bkshepherd/DaisySeedProjects/Hardware/GuitarPedal1590b-SMD/docs/images/Backside.png

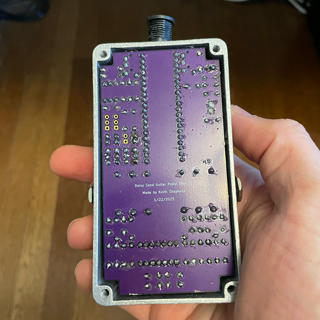
Hardware/GuitarPedal1590b-SMD/docs/images/Backside.png
