bkshepherd/DaisySeedProjects/Software/GuitarPedal/Effect-Modules/fm_keys_module.cpp

#include "fm_keys_module.h"
#include "../Util/audio_utilities.h"
#include <array>

using namespace bkshepherd;

// static VoiceManager<18> voice_handler; // starting with 1 voice for testing, 16 WORKS, 18 freezes
//  With added carrier env control, 16 glitches, 12 works
//  moved param changing to outside function, can run 18

static const auto s_metaData = [] {
    std::array<ParameterMetaData, FmKeysModule::PARAM_COUNT> params{};

    params[FmKeysModule::LEVEL] = {
        name : "Level",
        valueType : ParameterValueType::Float,
        defaultValue : {.float_value = 0.5f},
        knobMapping : 0,
        midiCCMapping : 14
    };

    params[FmKeysModule::RATIO] = {
        name : "Ratio",
        valueType : ParameterValueType::Float,
        defaultValue : {.float_value = 1.0f},
        knobMapping : 1,
        midiCCMapping : 15,
        minValue : 0,
        maxValue : 16
    };

    params[FmKeysModule::MOD_LEVEL] = {
        name : "ModLevel",
        valueType : ParameterValueType::Float,
        defaultValue : {.float_value = 0.2f},
        knobMapping : 2,
        midiCCMapping : 16
    };

    params[FmKeysModule::MOD_RATIO] = {
        name : "ModRatio",
        valueType : ParameterValueType::Float,
        defaultValue : {.float_value = 16.0f},
        knobMapping : 3,
        midiCCMapping : 17,
        minValue : 0,
        maxValue : 16
    };

    // TODO: Try fine/coarse step sizes of 0.5 (not in lighthouse yet?)
    params[FmKeysModule::CAR_ATTACK] = {
        name : "CarAttack",
        valueType : ParameterValueType::Float,
        defaultValue : {.float_value = 0.5f},
        knobMapping : 4,
        midiCCMapping : 18
    };

    params[FmKeysModule::CAR_DECAY] = {
        name : "CarDecay",
        valueType : ParameterValueType::Float,
        defaultValue : {.float_value = 0.5f},
        knobMapping : 5,
        midiCCMapping : 19
    };

    params[FmKeysModule::CAR_SUSTAIN] = {
        name : "CarSustain",
        valueType : ParameterValueType::Float,
        defaultValue : {.float_value = 0.5f},
        knobMapping : -1,
        midiCCMapping : 20
    };

    params[FmKeysModule::CAR_RELEASE] = {
        name : "CarRelease",
        valueType : ParameterValueType::Float,
        defaultValue : {.float_value = 0.5f},
        knobMapping : -1,
        midiCCMapping : 21
    };

    params[FmKeysModule::MOD_ATTACK] = {
        name : "ModAttack",
        valueType : ParameterValueType::Float,
        defaultValue : {.float_value = 0.5f},
        knobMapping : -1,
        midiCCMapping : 22
    };

    params[FmKeysModule::MOD_DECAY] = {
        name : "ModDecay",
        valueType : ParameterValueType::Float,
        defaultValue : {.float_value = 0.5f},
        knobMapping : -1,
        midiCCMapping : 23
    };

    params[FmKeysModule::MOD_SUSTAIN] = {
        name : "ModSustain",
        valueType : ParameterValueType::Float,
        defaultValue : {.float_value = 0.5f},
        knobMapping : -1,
        midiCCMapping : 24
    };

    params[FmKeysModule::MOD_RELEASE] = {
        name : "ModRelease",
        valueType : ParameterValueType::Float,
        defaultValue : {.float_value = 0.5f},
        knobMapping : -1,
        midiCCMapping : 25
    };

    return params;
}();

// Default Constructor
FmKeysModule::FmKeysModule() : BaseEffectModule(), m_freqMin(250.0f), m_freqMax(16000.0f), m_cachedEffectMagnitudeValue(1.0f) {
    // Set the name of the effect
    m_name = "FmKeys";

    // Setup the meta data reference for this Effect
    m_paramMetaData = s_metaData.data();

    // Initialize Parameters for this Effect
    this->InitParams(static_cast<int>(s_metaData.size()));
}

// Destructor
FmKeysModule::~FmKeysModule() {
    // No Code Needed
}

void FmKeysModule::Init(float sample_rate) {
    BaseEffectModule::Init(sample_rate);

    m_voice_handler.Init(sample_rate);
}

void FmKeysModule::ParameterChanged(int parameter_id) {

    if (parameter_id == LEVEL) {
        m_voice_handler.SetCarrierLevel(GetParameterAsFloat(LEVEL));

    } else if (parameter_id == RATIO) {
        float temp = GetParameterAsFloat(RATIO) * 2; // scale 0 to 16... 0 to 32
        int temp2 = static_cast<int>(temp);      // round by converting to int
        float temp3 = static_cast<float>(temp2);
        float float_val = temp3 / 2.0; // 0 to 16 increments of 0.5
        m_voice_handler.SetCarrierRatio(float_val);

    } else if (parameter_id == MOD_LEVEL) {
        m_voice_handler.SetModulatorLevel(GetParameterAsFloat(MOD_LEVEL) * GetParameterAsFloat(MOD_LEVEL)); // exponential

    } else if (parameter_id == MOD_RATIO) {
        float temp = GetParameterAsFloat(MOD_RATIO) * 2; // scale 0 to 16... 0 to 32
        int temp2 = static_cast<int>(temp);      // round by converting to int
        float temp3 = static_cast<float>(temp2);
        float float_val = temp3 / 2.0; // 0 to 16 increments of 0.5
        m_voice_handler.SetModulatorRatio(float_val);

    } else if (parameter_id == CAR_ATTACK) {
        m_voice_handler.SetCarrierAttack(GetParameterAsFloat(CAR_ATTACK) * GetParameterAsFloat(CAR_ATTACK) * 0.9999 + 0.0001); // exponential

    } else if (parameter_id == CAR_DECAY) {
        m_voice_handler.SetCarrierDecay(GetParameterAsFloat(CAR_DECAY) * GetParameterAsFloat(CAR_DECAY) * 0.9999 + 0.0001); // exponential

    } else if (parameter_id == CAR_SUSTAIN) {
        m_voice_handler.SetCarrierSustain(GetParameterAsFloat(CAR_SUSTAIN) * 0.999 + 0.001);

    } else if (parameter_id == CAR_RELEASE) {
        m_voice_handler.SetCarrierRelease(GetParameterAsFloat(CAR_RELEASE) * 0.999 + 0.001);

    } else if (parameter_id == MOD_ATTACK) {
        m_voice_handler.SetModAttack(GetParameterAsFloat(MOD_ATTACK) * GetParameterAsFloat(MOD_ATTACK) * 0.9999 + 0.0001); // exponential

    } else if (parameter_id == MOD_DECAY) {
        m_voice_handler.SetModDecay(GetParameterAsFloat(MOD_DECAY) * GetParameterAsFloat(MOD_DECAY) * 0.9999 + 0.0001); // exponential

    } else if (parameter_id == MOD_SUSTAIN) {
        m_voice_handler.SetModSustain(GetParameterAsFloat(MOD_SUSTAIN) * 0.999 + 0.001);

    } else if (parameter_id == MOD_RELEASE) {
        m_voice_handler.SetModRelease(GetParameterAsFloat(MOD_RELEASE) * 0.999 + 0.001);
    }
}

void FmKeysModule::OnNoteOn(float notenumber, float velocity) {
    // Note Off can come in as Note On w/ 0 Velocity
    if (velocity == 0.f) {
        m_voice_handler.OnNoteOff(notenumber, velocity);
    } else {
        m_voice_handler.OnNoteOn(notenumber, velocity);
    }
}

void FmKeysModule::OnNoteOff(float notenumber, float velocity) { m_voice_handler.OnNoteOff(notenumber, velocity); }

void FmKeysModule::ProcessMono(float in) {
    BaseEffectModule::ProcessMono(in);

    // float through_audioL = m_audioLeft;

    float sum = 0.f;
    sum = m_voice_handler.Process() * 0.3f; // 0.3 for volume reduction
    m_audioLeft = sum;
    m_audioRight = m_audioLeft;
}

void FmKeysModule::ProcessStereo(float inL, float inR) {
    // Calculate the mono effect
    ProcessMono(inL);
}

float FmKeysModule::GetBrightnessForLED(int led_id) const {
    float value = BaseEffectModule::GetBrightnessForLED(led_id);

    if (led_id == 1) {
        return value * m_cachedEffectMagnitudeValue;
    }

    return value;
}
