bkshepherd/DaisySeedProjects/Software/GuitarPedal/Effect-Modules/nam_module.cpp

#include "nam_module.h"
#include "../Util/audio_utilities.h"
#include "../dependencies/RTNeural-NAM-modified/wavenet/wavenet_model.hpp"
#include "Nam/model_data_nam.h"
#include <RTNeural/RTNeural.h>
#include <q/fx/biquad.hpp>
#include <array>

using namespace bkshepherd;

constexpr uint8_t NUM_FILTERS_NAM = 3;

const float minGain = -10.f;
const float maxGain = 10.f;

const float centerFrequencyNam[NUM_FILTERS_NAM] = {110.f, 900.f, 4000.f}; // Experiment with these freqs and q values
const float q_nam[NUM_FILTERS_NAM] = {.7f, .7f, .7f};

cycfi::q::peaking filter_nam[NUM_FILTERS_NAM] = {{0, centerFrequencyNam[0], 48000, q_nam[0]},
                                                 {0, centerFrequencyNam[1], 48000, q_nam[1]},
                                                 {0, centerFrequencyNam[2], 48000, q_nam[2]}};

// This must match the length of the model_collection_nam array in model_data_nam.h
const size_t k_numModels = 10;

static const char *s_modelBinNames[k_numModels] = {
    "Mesa", "Match30", "DumHighG", "DumLowG", "Ethos", "Splawn", "PRSArch", "JCM800", "SansAmp", "BE-100",
};
struct NAMMathsProvider {
#if RTNEURAL_USE_EIGEN
    template <typename Matrix> static auto tanh(const Matrix &x) {
        // See: math_approx::tanh<3>
        const auto x_poly = x.array() * (1.0f + 0.183428244899f * x.array().square());
        return x_poly.array() * (x_poly.array().square() + 1.0f).array().rsqrt();
        // return x.array().tanh(); // Tried using Eigen's built in tanh(), also works, failed on the same larger models as above
        // custom tanh
    }
#elif RTNEURAL_USE_XSIMD
    template <typename T> static T tanh(const T &x) { return math_approx::tanh<3>(x); }
#endif
};

static const auto s_metaData = [] {
    std::array<ParameterMetaData, NamModule::PARAM_COUNT> params{};

    params[NamModule::GAIN] = {
        name : "Gain",
        valueType : ParameterValueType::Float,
        valueCurve : ParameterValueCurve::Log,
        defaultValue : {.float_value = 0.5f},
        knobMapping : 0,
        midiCCMapping : 14,
    };

    params[NamModule::LEVEL] = {
        name : "Level",
        valueType : ParameterValueType::Float,
        defaultValue : {.float_value = 0.5f},
        knobMapping : 1,
        midiCCMapping : 15
    };

    params[NamModule::MODEL] = {
        name : "Model",
        valueType : ParameterValueType::Binned,
        valueBinCount : k_numModels,
        valueBinNames : s_modelBinNames,
        defaultValue : {.uint_value = 0},
        knobMapping : 2,
        midiCCMapping : 16
    };

    params[NamModule::BASS] = {
        name : "Bass",
        valueType : ParameterValueType::Float,
        valueBinCount : 0,
        defaultValue : {.float_value = 0.0f},
        knobMapping : 3,
        midiCCMapping : 17,
        minValue : static_cast<int>(minGain),
        maxValue : static_cast<int>(maxGain)
    };

    params[NamModule::MID] = {
        name : "Mid",
        valueType : ParameterValueType::Float,
        valueBinCount : 0,
        defaultValue : {.float_value = 0.0f},
        knobMapping : 4,
        midiCCMapping : 18,
        minValue : static_cast<int>(minGain),
        maxValue : static_cast<int>(maxGain)
    };

    params[NamModule::TREBLE] = {
        name : "Treble",
        valueType : ParameterValueType::Float,
        valueBinCount : 0,
        defaultValue : {.float_value = 0.0f},
        knobMapping : 5,
        midiCCMapping : 19,
        minValue : static_cast<int>(minGain),
        maxValue : static_cast<int>(maxGain)
    };

    params[NamModule::NEURAL_MODEL] = {
        name : "NeuralModel",
        valueType : ParameterValueType::Bool,
        valueBinCount : 0,
        defaultValue : {.uint_value = 1},
        knobMapping : -1,
        midiCCMapping : 20
    };

    params[NamModule::EQ] = {
        name : "EQ",
        valueType : ParameterValueType::Bool,
        valueBinCount : 0,
        defaultValue : {.uint_value = 1},
        knobMapping : -1,
        midiCCMapping : 21
    };

    return params;
}();

// NOTE NAM Standard arch?
/*
using Dilations = wavenet::Dilations<1, 2, 4, 8, 16, 32, 64, 128, 256, 512>;
wavenet::Wavenet_Model<float,
                       1,
                       wavenet::Layer_Array<float, 1, 1, 8, 16, 3, Dilations, false, NAMMathsProvider>,
                       wavenet::Layer_Array<float, 16, 1, 1, 8, 3, Dilations, true, NAMMathsProvider>>
    rtneural_wavenet;
*/

// NOTE NAM "Pico" (unnoficial model type)
using Dilations = wavenet::Dilations<1, 2, 4, 8, 16, 32, 64>;
using Dilations2 = wavenet::Dilations<128, 256, 512, 1, 2, 4, 8, 16, 32, 64, 128, 256, 512>;
wavenet::Wavenet_Model<float, 1, wavenet::Layer_Array<float, 1, 1, 2, 2, 3, Dilations, false, NAMMathsProvider>,
                       wavenet::Layer_Array<float, 2, 1, 1, 2, 3, Dilations2, true, NAMMathsProvider>>
    rtneural_wavenet;

// NOTES:
// nano models:
//   Seems to run (verify sound) for Samplerate 32kHz, Blocksize 64, 1 sample at a time
//   Freezes at Samplerate 48kHz, Blocksize 64, 1 sample at a time
//   Runs at samplerate 32kHz, Blocksize 48, 1 sample, verify sound

// Default Constructor
NamModule::NamModule()
    : BaseEffectModule(), m_gainMin(0.0f), m_gainMax(2.0f), m_levelMin(0.0f), m_levelMax(2.0f), m_cachedEffectMagnitudeValue(1.0f) {
    // Set the name of the effect
    m_name = "NAM";

    // Setup the meta data reference for this Effect
    m_paramMetaData = s_metaData.data();

    // Initialize Parameters for this Effect
    this->InitParams(static_cast<int>(s_metaData.size()));
}

// Destructor
NamModule::~NamModule() {
    // No Code Needed
}

void NamModule::Init(float sample_rate) {
    BaseEffectModule::Init(sample_rate);
    setupWeightsNam(); // in the model data nam .h file
    SelectModel();

    filter_nam[0].config(GetParameterAsFloat(BASS), centerFrequencyNam[0], sample_rate, q_nam[0]);
    filter_nam[1].config(GetParameterAsFloat(MID), centerFrequencyNam[1], sample_rate, q_nam[1]);
    filter_nam[2].config(GetParameterAsFloat(TREBLE), centerFrequencyNam[2], sample_rate, q_nam[2]);
}

void NamModule::ParameterChanged(int parameter_id) {
    if (parameter_id == MODEL) { // Change Model
        SelectModel();
    } else if (parameter_id == BASS) {
        filter_nam[0].config(GetParameterAsFloat(BASS), centerFrequencyNam[0], GetSampleRate(), q_nam[0]);
    } else if (parameter_id == MID) {
        filter_nam[1].config(GetParameterAsFloat(MID), centerFrequencyNam[1], GetSampleRate(), q_nam[1]);
    } else if (parameter_id == TREBLE) {
        filter_nam[2].config(GetParameterAsFloat(TREBLE), centerFrequencyNam[2], GetSampleRate(), q_nam[2]);
    }
}

void NamModule::SelectModel() {
    const int modelIndex = GetParameterAsBinnedValue(MODEL) - 1;

    if (m_currentModelindex != modelIndex) {
        // Temporarily disable output as we switch models
        m_muteOutput = true;
        rtneural_wavenet.load_weights(model_collection_nam[modelIndex].weights);
        static constexpr size_t N = 1; // number of samples sent through model at once
        rtneural_wavenet.prepare(N);   // This is needed, including this allowed the led to come on before freezing
        rtneural_wavenet.prewarm();    // Note: looks like this just sends some 0's through the model
        m_currentModelindex = modelIndex;
        // Re-enable output
        m_muteOutput = false;
    }
}

void NamModule::ProcessMono(float in) {
    // When switching models, we stop processing temporarily and mute the output
    if (m_muteOutput) {
        m_audioLeft = m_audioRight = 0.0f;
        return;
    }

    BaseEffectModule::ProcessMono(in);

    float ampOut;
    float input_arr[1] = {0.0}; // Neural Net Input
    input_arr[0] = m_audioLeft * (m_gainMin + (m_gainMax - m_gainMin) * GetParameterAsFloat(GAIN));

    // NEURAL MODEL //
    if (GetParameterAsBool(NEURAL_MODEL)) {
        ampOut =
            rtneural_wavenet.forward(input_arr[0]) * 0.4; // TODO Try this again, was sending the whole array, wants just the float

        // Apply level normalization factor
        if (m_currentModelindex >= 0 && m_currentModelindex < static_cast<int>(k_numModels)) {
            ampOut *= model_collection_nam[m_currentModelindex].levelAdjust;
        }
    } else {
        ampOut = input_arr[0];
    }

    // Apply 3 band EQ
    if (GetParameterAsBool(EQ)) {
        for (uint8_t i = 0; i < NUM_FILTERS_NAM; i++) {
            ampOut = filter_nam[i](ampOut);
        }
    }

    const float level = m_levelMin + (GetParameterAsFloat(LEVEL) * (m_levelMax - m_levelMin));

    m_audioRight = m_audioLeft = ampOut * level;
}

void NamModule::ProcessStereo(float inL, float inR) {
    // Calculate the mono effect
    ProcessMono(inL);

    // NOTE: Running the Neural Nets in stereo is currently not feasible due to processing limitations, this will remain a MONO ONLY
    // effect for now.
    //       The left channel output is copied to the right output, but the right input is ignored in this effect module.

    // Do the base stereo calculation (which resets the right signal to be the inputR instead of combined mono)
    // BaseEffectModule::ProcessStereo(m_audioLeft, inR);

    // m_audioRight = m_audioLeft;

    // Use the same magnitude as already calculated for the Left Audio
    // m_audioRight = m_audioRight * m_cachedEffectMagnitudeValue;
}

float NamModule::GetBrightnessForLED(int led_id) const {
    float value = BaseEffectModule::GetBrightnessForLED(led_id);

    if (led_id == 1) {
        return value * m_cachedEffectMagnitudeValue;
    }

    return value;
}
