bkshepherd/DaisySeedProjects/Software/GuitarPedal/Effect-Modules/metro_module.cpp

#include "metro_module.h"
#include "../Util/audio_utilities.h"
#include <array>

using namespace bkshepherd;

void Metronome::Init(float freq, float sample_rate) {
    freq_ = freq;
    phs_ = 0.0f;
    sample_rate_ = sample_rate;
    phs_inc_ = (TWOPI_F * freq_) / sample_rate_;
}

uint8_t Metronome::Process() {
    phs_ += phs_inc_;
    if (phs_ >= TWOPI_F) {
        phs_ -= TWOPI_F;
        return 1;
    }
    return 0;
}

void Metronome::SetFreq(float freq) {
    freq_ = freq;
    phs_inc_ = (TWOPI_F * freq_) / sample_rate_;
}

uint16_t Metronome::GetQuadrant() {
    if (phs_ < PI_F / 2.0)
        return 0;
    else if (phs_ >= PI_F / 2.0 && phs_ < PI_F)
        return 1;
    else if (phs_ >= PI_F && phs_ < PI_F * 3.0 / 2.0)
        return 2;
    else
        return 3;
}

uint16_t Metronome::GetQuadrant16() {
    float phase = phs_;
    if (phase > TWOPI_F)
        phase = TWOPI_F;

    uint16_t quadrant = (uint16_t)(phase * 16.0 / TWOPI_F);
    return quadrant;
}

static const char *TimeSignatureLabels[3] = {"4/4", "3/4", "2/4"};
static const uint16_t TimeSignatureBase[3] = {4, 3, 2};

constexpr uint32_t minTempo = 35;
constexpr uint32_t maxTempo = 250;

static const auto s_metaData = [] {
    std::array<ParameterMetaData, MetroModule::PARAM_COUNT> params{};

    params[MetroModule::TEMPO] = {
        name : "Tempo",
        valueType : ParameterValueType::Float,
        valueBinCount : 0,
        defaultValue : {.float_value = 165.f},
        knobMapping : 0,
        midiCCMapping : 23,
        minValue : minTempo,
        maxValue : maxTempo
    };

    params[MetroModule::MIX] = {
        name : "Mix",
        valueType : ParameterValueType::Float,
        valueBinCount : 0,
        defaultValue : {.float_value = 0.08f},
        knobMapping : 1,
        midiCCMapping : 21
    };

    params[MetroModule::METER] = {
        name : "Meter",
        valueType : ParameterValueType::Binned,
        valueBinCount : 3,
        valueBinNames : TimeSignatureLabels,
        defaultValue : {.uint_value = 0},
        knobMapping : 2,
        midiCCMapping : -1
    };

    return params;
}();

// Default Constructor
MetroModule::MetroModule() : BaseEffectModule(), m_levelMin(0.0f), m_levelMax(1.0f) {
    // Set the name of the effect
    m_name = "Metronome";

    // Setup the meta data reference for this Effect
    m_paramMetaData = s_metaData.data();

    // Initialize Parameters for this Effect
    this->InitParams(static_cast<int>(s_metaData.size()));
}

// Destructor
MetroModule::~MetroModule() {
    // No Code Needed
}

void MetroModule::Init(float sample_rate) {
    BaseEffectModule::Init(sample_rate);
    m_quadrant = 0;
    m_direction = 0;
    m_beat = 0;
    m_timeSignature = TimeSignature::meter4x4;

    // set oscillator
    m_osc.Init(sample_rate);
    m_osc.SetWaveform(Oscillator::WAVE_POLYBLEP_SAW);
    m_osc.SetFreq(440.0f);
    m_osc.SetAmp(0.02f);

    // Set envelope
    m_env.Init(sample_rate);
    m_env.SetTime(ADSR_SEG_ATTACK, .1);
    m_env.SetTime(ADSR_SEG_DECAY, .2);
    m_env.SetTime(ADSR_SEG_RELEASE, .01);
    m_env.SetSustainLevel(.5);

    // Set metronome
    m_bpm = static_cast<uint32_t>(GetParameterAsFloat(TEMPO));
    const float freq = tempo_to_freq(m_bpm);
    m_metro.Init(freq, sample_rate);
}

void MetroModule::ParameterChanged(int parameter_id) {
    if (parameter_id == TEMPO) {
        m_bpm = static_cast<uint32_t>(GetParameterAsFloat(TEMPO));
    }
}

float MetroModule::Process() {
    const float freq = tempo_to_freq(m_bpm);

    uint16_t tsig = GetParameterAsBinnedValue(METER) - 1;
    if (tsig != m_timeSignature)
        m_timeSignature = static_cast<TimeSignature>(tsig);

    if (freq != m_metro.GetFreq())
        m_metro.SetFreq(freq);

    if (m_metro.Process()) {
        m_beat++;
        m_osc.SetFreq((m_beat % (TimeSignatureBase[static_cast<uint16_t>(m_timeSignature)]) == 0) ? 440.0f : 220.0f);
        m_direction = !m_direction;
    }

    m_quadrant = m_metro.GetQuadrant16();

    float sig = m_osc.Process();
    float env_out = m_env.Process(m_quadrant < 2);
    return sig * env_out;
}

void MetroModule::ProcessMono(float in) {
    BaseEffectModule::ProcessMono(in);
    float sig = Process();
    // Adjust the level
    float level = (m_levelMin + (GetParameterAsFloat(MIX) * (m_levelMax - m_levelMin)));
    m_audioLeft = sig * level + in * (1.0f - level);
    m_audioRight = m_audioLeft;
}

void MetroModule::ProcessStereo(float inL, float inR) {
    BaseEffectModule::ProcessStereo(inL, inR);
    float sig = Process();
    // Adjust the level
    float level = (m_levelMin + (GetParameterAsFloat(MIX) * (m_levelMax - m_levelMin)));
    m_audioLeft = sig * level + inL * (1.0f - level);
    m_audioRight = sig * level + inR * (1.0f - level);
}

void MetroModule::SetTempo(uint32_t bpm) { m_bpm = std::clamp(bpm, minTempo, maxTempo); }

float MetroModule::GetBrightnessForLED(int led_id) const {
    float value = BaseEffectModule::GetBrightnessForLED(led_id);

    if (led_id == 1) {
        return 1.0f - (m_quadrant / 16.0);
    }

    return value;
}

void MetroModule::DrawUI(OneBitGraphicsDisplay &display, int currentIndex, int numItemsTotal, Rectangle boundsToDrawIn,
                         bool isEditing) {
    BaseEffectModule::DrawUI(display, currentIndex, numItemsTotal, boundsToDrawIn, isEditing);

    // Show tempo in BPM
    char strbuff[64];
    int topRowHeight = boundsToDrawIn.GetHeight() / 2;

    sprintf(strbuff, "%s %lu BPM", TimeSignatureLabels[static_cast<uint16_t>(m_timeSignature)], m_bpm);
    boundsToDrawIn.RemoveFromTop(topRowHeight);
    display.WriteStringAligned(strbuff, Font_11x18, boundsToDrawIn, Alignment::centered, true);

    /*
      sprintf(strbuff, " %d ", m_quadrant);
      boundsToDrawIn.RemoveFromTop(topRowHeight);
      display.WriteStringAligned(strbuff, Font_11x18, boundsToDrawIn, Alignment::centered, true);
    */

    // Show metronome indicator
    int pos_inc = boundsToDrawIn.GetWidth() / 16;
    uint16_t position = m_direction == 0 ? m_quadrant * pos_inc : -(m_quadrant - 15) * pos_inc;

    Rectangle r(position, topRowHeight - 7, pos_inc - 1, 10);
    // display.DrawRect(r, true, (m_quadrant % 4) == 0);
    display.DrawRect(r, true, true);
}
