bkshepherd/DaisySeedProjects/Software/GuitarPedal/Effect-Modules/delay_module.h

#pragma once
#ifndef DELAY_MODULE_H
#define DELAY_MODULE_H

#include "Delays/delayline_reverse.h"
#include "Delays/delayline_revoct.h"
#include "../Util/tape_modulator.h"
#include "base_effect_module.h"
#include "daisysp.h"
#include <stdint.h>
#ifdef __cplusplus

/** @file _delay_module.h */

using namespace daisysp;

// Delay Max Definitions (Assumes 48kHz samplerate)
constexpr size_t MAX_DELAY_NORM =
    static_cast<size_t>(48000.0f * 8.f); // 4 second max delay // Increased the max to 8 seconds, got horrible pop noise when set to 4
                                         // seconds, increasing buffer size fixes it for some reason. TODO figure out why?
constexpr size_t MAX_DELAY_REV =
    static_cast<size_t>(48000.0f * 8.f); // 8 second max delay (needs to be double for reverse, since read/write pointers are going
                                         // opposite directions in the buffer)
constexpr size_t MAX_DELAY_SPREAD = static_cast<size_t>(4800.0f); //  50 ms for Spread effect

// This is the core delay struct, which actually includes two delays,
// one for forwared/octave, and one for reverse. This is required
// because the reverse delayline needs to be double the size of the
// normal delayline to have the same range of the Time control. Both
// delays are processed, with the main delay feeding into the reverse
// delay to allow for Reverse Octave. A lowpass filter is included in
// the feedback loop, which can tame the harsh high frequencies of the
// octave delay, or create a "fading into the distance" effect for the
// forward and reverse delays. A "level" param is included for modulation
// of the output volume, for stereo panning.
struct delayRevOct {
    DelayLineRevOct<float, MAX_DELAY_NORM> *del;
    DelayLineReverse<float, MAX_DELAY_REV> *delreverse;
    float currentDelay;
    float delayTarget;
    float feedback = 0.0;
    float active = false;
    bool reverseMode = false;
    Tone toneOctLP;            // Low Pass
    float level = 1.0;         // Level multiplier of output, added for stereo modulation
    float level_reverse = 1.0; // Level multiplier of output, added for stereo modulation
    bool dual_delay = false;
    bool secondTapOn = false;

    float Process(float in) {
        // set delay times
        fonepole(currentDelay, delayTarget, .0002f);
        del->SetDelay(currentDelay);
        delreverse->SetDelay1(currentDelay);

        float del_read = del->Read();

        float read_reverse = delreverse->ReadRev(); // REVERSE

        float read =
            toneOctLP.Process(del_read); // LP filter, tames harsh high frequencies on octave, has fading effect for normal/reverse

        float secondTap = 0.0;
        if (secondTapOn) {
            secondTap = del->ReadSecondTap();
        }
        // float read2 = delreverse->ReadFwd();
        if (active) {
            del->Write((feedback * read) + in);
            delreverse->Write((feedback * read) +
                              in); // Writing the read from fwd/oct delay line allows for combining oct and rev for reverse octave!
            // delreverse->Write((feedback * read2) + in);
        } else {
            del->Write(feedback * read); // if not active, don't write any new sound to buffer
            delreverse->Write(feedback * read);
            // delreverse->Write((feedback * read2));
        }

        // TODO Figure out how to do dotted eighth with reverse

        if (dual_delay) {
            return read_reverse * level_reverse * 0.5 +
                   (read + secondTap) * level * 0.5; // Half the volume to keep total level consistent
        } else if (reverseMode) {
            return read_reverse * level_reverse;
        } else {
            return (read + secondTap) * level;
        }
    }
};

// For stereo spread setting (delay the right channel signal from 0 to 50ms)
//    A short, zero feedback (one repeat) delay for stereo spread

struct delay_spread {
    DelayLine<float, MAX_DELAY_SPREAD> *del;
    float currentDelay;
    float delayTarget;
    float active = false;

    float Process(float in) {
        // set delay times
        fonepole(currentDelay, delayTarget, .0002f);
        del->SetDelay(currentDelay);

        float read = del->Read();
        if (active) {
            del->Write(in);
        }

        return read;
    }
};

namespace bkshepherd {

class DelayModule : public BaseEffectModule {
  public:
    enum Param {
        DELAY_TIME = 0,
        D_FEEDBACK,
        DELAY_MIX,
        DELAY_MODE,
        DELAY_TYPE,
        DELAY_LPF,
        D_SPREAD,
        MOD_AMT,
        MOD_RATE,
        MOD_PARAM,
        MOD_WAVE,
        SYNC_MOD_F,
        PARAM_COUNT
    };

    DelayModule();
    ~DelayModule();

    void Init(float sample_rate) override;
    void UpdateLEDRate();
    void CalculateDelayMix();
    void ParameterChanged(int parameter_id) override;
    void ProcessModulation();
    void ProcessMono(float in) override;
    void ProcessStereo(float inL, float inR) override;
    void SetTempo(uint32_t bpm) override;
    float GetBrightnessForLED(int led_id) const override;
    int GetMappedParameterIDForKnob(int knob_id) const override;
    void AlternateFootswitchHeldFor1Second() override;
    void DrawUI(OneBitGraphicsDisplay &display, int currentIndex, int numItemsTotal, Rectangle boundsToDrawIn,
                bool isEditing) override;

  private:
    float m_delaylpFreqMin;
    float m_delaylpFreqMax;
    float m_delaySamplesMin;
    float m_delaySamplesMax;
    float m_delaySpreadMin;
    float m_delaySpreadMax;
    float m_pdelRight_out;
    float m_currentMod;

    Oscillator modOsc;
    float m_modOscFreqMin;
    float m_modOscFreqMax;
    TapeModulator modTape;

    // Delays
    delayRevOct delayLeft;
    delayRevOct delayRight;
    delay_spread delaySpread;

    // Mix params
    float delayWetMix = 0.5;
    float delayDryMix = 0.5;
    float WetMix = 0.5;
    float DryMix = 0.5;

    float _level = 1.0;

    float effect_samplerate;

    // Oscillator for blinking tempo LED
    Oscillator led_osc;
    float m_LEDValue;

    // Shift layer for alternate knob mapping
    bool m_shiftModeActive = false;
        bool m_shiftModeToggled = false;  // Gate to prevent multiple toggles during single hold
};
} // namespace bkshepherd
#endif
#endif
