bkshepherd/DaisySeedProjects/Software/GuitarPedal/Effect-Modules/autopan_module.cpp

#include "autopan_module.h"
#include "../Util/audio_utilities.h"
#include <array>

using namespace bkshepherd;

static const char *s_waveBinNames[8] = {"Sine", "Triangle", "Saw", "Ramp", "Square", "Poly Tri", "Poly Saw", "Poly Sqr"};

static const auto s_metaData = [] {
    std::array<ParameterMetaData, AutoPanModule::PARAM_COUNT> params{};

    params[AutoPanModule::WET] = {
        name : "Wet",
        valueType : ParameterValueType::Float,
        defaultValue : {.float_value = 1.0f},
        knobMapping : 0,
        midiCCMapping : 20
    };

    params[AutoPanModule::OSC_WAVE] = {
        name : "Osc Wave",
        valueType : ParameterValueType::Binned,
        valueBinCount : 8,
        valueBinNames : s_waveBinNames,
        defaultValue : {.uint_value = 0},
        knobMapping : 2,
        midiCCMapping : 21
    };

    params[AutoPanModule::OSC_FREQ] = {
        name : "Osc Freq",
        valueType : ParameterValueType::Float,
        defaultValue : {.float_value = 0.1f},
        knobMapping : 1,
        midiCCMapping : 1
    };

    params[AutoPanModule::STEREO] = {
        name : "Stereo",
        valueType : ParameterValueType::Bool,
        defaultValue : {.uint_value = 0},
        knobMapping : 3,
        midiCCMapping : 23
    };

    return params;
}(); // 0 is Mono (even if fed stereo) 1 is Stereo

// Default Constructor
AutoPanModule::AutoPanModule()
    : BaseEffectModule(), m_freqOscFreqMin(0.01f), m_freqOscFreqMax(4.0f)

{
    // Set the name of the effect
    m_name = "AutoPan";

    // Setup the meta data reference for this Effect
    m_paramMetaData = s_metaData.data();

    // Initialize Parameters for this Effect
    this->InitParams(static_cast<int>(s_metaData.size()));
}

// Destructor
AutoPanModule::~AutoPanModule() {
    // No Code Needed
}

void AutoPanModule::Init(float sample_rate) {
    BaseEffectModule::Init(sample_rate);

    m_freqOsc.Init(sample_rate);
}

void AutoPanModule::ProcessMono(float in) {
    BaseEffectModule::ProcessMono(in);

    // Calculate Pan Oscillation
    m_freqOsc.SetWaveform(GetParameterAsBinnedValue(OSC_WAVE) - 1);
    m_freqOsc.SetAmp(0.5f);
    m_freqOsc.SetFreq(m_freqOscFreqMin + (GetParameterAsFloat(OSC_FREQ) * m_freqOscFreqMax));
    float mod = 0.5f + m_freqOsc.Process();

    if (GetParameterAsFloat(OSC_FREQ) <= 0.01f) {
        mod = 0.5f;
        m_pan = mod;
    }

    // Ease the m_pan value into it's target to avoid clipping
    fonepole(m_pan, mod, .001f);

    float r = sqrtf(2.0f) / 2.0f;
    float scaled = m_pan * HALFPI_F;
    float angle = scaled / 2.0f;

    float audioLeftWet = m_audioLeft * (r * (cosf(angle) - sinf(angle)));
    float audioRightWet = m_audioRight * (r * (cosf(angle) + sinf(angle)));

    // Handle the wet / dry mix
    m_audioLeft = audioLeftWet * GetParameterAsFloat(WET) + m_audioLeft * (1.0f - GetParameterAsFloat(WET));
    m_audioRight = audioRightWet * GetParameterAsFloat(WET) + m_audioRight * (1.0f - GetParameterAsFloat(WET));
}

void AutoPanModule::ProcessStereo(float inL, float inR) {
    // Calculate the mono effect
    ProcessMono(inL);

    // If we are processing in mono only no need to do anything
    if (!GetParameterAsBool(STEREO)) {
        return;
    }

    // Do the base stereo calculation (which resets both signals even though we calculated it in mono)
    BaseEffectModule::ProcessStereo(inL, inR);

    // Calculate Stereo Effect
    float adjustedPan = (m_pan - 0.5f) * 2.0f;
    float mSignal = 0.5f * (m_audioLeft + m_audioRight);
    float sSignal = m_audioLeft - m_audioRight;

    float audioLeftWet = 0.5f * (1.0f + adjustedPan) * mSignal + sSignal;
    float audioRightWet = 0.5f * (1.0f - adjustedPan) * mSignal - sSignal;

    // Handle the wet / dry mix
    m_audioLeft = audioLeftWet * GetParameterAsFloat(WET) + m_audioLeft * (1.0f - GetParameterAsFloat(WET));
    m_audioRight = audioRightWet * GetParameterAsFloat(WET) + m_audioRight * (1.0f - GetParameterAsFloat(WET));
}

void AutoPanModule::SetTempo(uint32_t bpm) {
    float freq = tempo_to_freq(bpm);

    // Adjust the frequency into a range that makes sense for the effect
    freq = freq / 4.0f;

    if (freq <= m_freqOscFreqMin) {
        SetParameterAsMagnitude(2, 0.0f);
    } else if (freq >= m_freqOscFreqMax) {
        SetParameterAsMagnitude(2, 1.0f);
    } else {
        float magnitude = static_cast<float>(freq - m_freqOscFreqMin) / static_cast<float>(m_freqOscFreqMax - m_freqOscFreqMin);
        SetParameterAsMagnitude(2, magnitude);
    }
}

float AutoPanModule::GetBrightnessForLED(int led_id) const {
    float value = BaseEffectModule::GetBrightnessForLED(led_id);

    if (led_id == 1) {
        return value * m_pan;
    }

    return value;
}

void AutoPanModule::UpdateUI(float elapsedTime) {
    // Let the base class do it's thing.
    BaseEffectModule::UpdateUI(elapsedTime);
}

void AutoPanModule::DrawUI(OneBitGraphicsDisplay &display, int currentIndex, int numItemsTotal, Rectangle boundsToDrawIn,
                           bool isEditing) {
    // Let the base class do it's thing.
    BaseEffectModule::DrawUI(display, currentIndex, numItemsTotal, boundsToDrawIn, isEditing);

    // If the effect isn't enabled don't draw the custom UI
    if (!IsEnabled()) {
        return;
    }

    int lineY = (boundsToDrawIn.GetHeight() / 5.0f) * 3;
    int lineStartX = boundsToDrawIn.GetX();
    int lineEndX = boundsToDrawIn.GetRight();

    // calculate the pan location
    int panLocationX = lineStartX + (m_pan * (boundsToDrawIn.GetWidth() - 20));

    // Draws a line and a ball where the pan is currently located between L/R side
    display.DrawLine(lineStartX + 10, lineY, lineEndX - 10, lineY, true);
    display.DrawCircle(panLocationX + 10, lineY, 3, true);
    display.SetCursor(lineStartX, lineY - 4);
    display.WriteChar('L', Font_6x8, true);
    display.SetCursor(lineEndX - 6, lineY - 4);
    display.WriteChar('R', Font_6x8, true);
}
