bkshepherd/DaisySeedProjects/Software/GuitarPedal/Effect-Modules/compressor_module.cpp

#include "compressor_module.h"
#include <array>

using namespace bkshepherd;

static const auto s_metaData = [] {
    std::array<ParameterMetaData, CompressorModule::PARAM_COUNT> params{};

    params[CompressorModule::LEVEL] = {
        name : "Level",
        valueType : ParameterValueType::Float,
        valueBinCount : 0,
        defaultValue : {.float_value = 0.5f},
        knobMapping : 0,
        midiCCMapping : -1
    };

    params[CompressorModule::RATIO] = {
        name : "Ratio",
        valueType : ParameterValueType::Float,
        valueBinCount : 0,
        defaultValue : {.float_value = 0.5f},
        knobMapping : 1,
        midiCCMapping : -1
    };

    params[CompressorModule::THRESHOLD] = {
        name : "Thresh",
        valueType : ParameterValueType::Float,
        valueBinCount : 0,
        defaultValue : {.float_value = 0.5f},
        knobMapping : 2,
        midiCCMapping : -1
    };

    params[CompressorModule::ATTACK] = {
        name : "Attack",
        valueType : ParameterValueType::Float,
        valueBinCount : 0,
        defaultValue : {.float_value = 0.5f},
        knobMapping : 3,
        midiCCMapping : -1
    };

    params[CompressorModule::RELEASE] = {
        name : "Release",
        valueType : ParameterValueType::Float,
        valueBinCount : 0,
        defaultValue : {.float_value = 0.5f},
        knobMapping : 4,
        midiCCMapping : -1
    };

    return params;
}();

// Default Constructor
CompressorModule::CompressorModule() : BaseEffectModule() {
    // Set the name of the effect
    m_name = "Comp";

    // Setup the meta data reference for this Effect
    m_paramMetaData = s_metaData.data();

    // Initialize Parameters for this Effect
    this->InitParams(static_cast<int>(s_metaData.size()));
}

// Destructor
CompressorModule::~CompressorModule() {
    // No Code Needed
}

void CompressorModule::Init(float sample_rate) {
    BaseEffectModule::Init(sample_rate);

    m_compressor.Init(sample_rate);
}

void CompressorModule::ParameterChanged(int parameter_id) {
    switch (parameter_id) {
    case RATIO: {
        const float ratioMin = 1.0f;
        const float ratioMax = 40.0f;
        float ratio = ratioMin + (GetParameterAsFloat(RATIO) * (ratioMax - ratioMin));
        m_compressor.SetRatio(ratio);
        break;
    }
    case THRESHOLD: {
        const float thresholdMin = 0.0f;
        const float thresholdMax = 80.0f;
        float threshold = thresholdMin + (GetParameterAsFloat(THRESHOLD) * (thresholdMax - thresholdMin));
        // This is in dB so it is supposed to be 0dB to -80dB
        m_compressor.SetThreshold(-threshold);
        break;
    }
    case ATTACK: {
        const float attackMin = 0.001f;
        const float attackMax = 10.0f;
        float attack = attackMin + (GetParameterAsFloat(ATTACK) * (attackMax - attackMin));
        m_compressor.SetAttack(attack);
        break;
    }
    case RELEASE: {
        const float releaseMin = 0.001f;
        const float releaseMax = 10.0f;
        float release = releaseMin + (GetParameterAsFloat(RELEASE) * (releaseMax - releaseMin));
        m_compressor.SetRelease(release);
        break;
    }
    }
}

void CompressorModule::ProcessMono(float in) {
    const float compressor_out = m_compressor.Process(in);

    const float level = m_levelMin + (GetParameterAsFloat(LEVEL) * (m_levelMax - m_levelMin));

    m_audioLeft = compressor_out * level;
    m_audioRight = m_audioLeft;
}

void CompressorModule::ProcessStereo(float inL, float inR) {
    // Calculate the mono effect
    ProcessMono(inL);
}

float CompressorModule::GetBrightnessForLED(int led_id) const {
    float value = BaseEffectModule::GetBrightnessForLED(led_id);

    // TODO: Use gain for the LED
    // if (led_id == 1)
    // {
    //     return value * m_compressor.GetGain();
    // }

    return value;
}
