bkshepherd/DaisySeedProjects/Software/GuitarPedal/Effect-Modules/Delays/delayline_revoct.h

#pragma once
#ifndef DELAYLINE_REVOCT_H
#define DELAYLINE_REVOCT_H
#include <stdint.h>
#include <stdlib.h>
// namespace daisysp
//{
/** Simple Delay line.
November 2019

Converted to Template December 2019

declaration example: (1 second of floats)

DelayLine<float, SAMPLE_RATE> del;

By: shensley
*/
template <typename T, size_t max_size> class DelayLineRevOct {
  public:
    DelayLineRevOct() {}
    ~DelayLineRevOct() {}
    /** initializes the delay line by clearing the values within, and setting delay to 1 sample.
     */
    void Init() { Reset(); }
    /** clears buffer, sets write ptr to 0, and delay to 1 sample.
     */
    void Reset() {
        for (size_t i = 0; i < max_size; i++) {
            line_[i] = T(0);
        }
        write_ptr_ = 0;
        delay_ = 1;
        speed = 1;
        delay_secondTap = 1;
        delay_float = 1.0;
        secondTapFraction = 0.0;
    }

    inline void setOctave(bool isOctave) {
        if (isOctave) {
            speed = 2;
        } else {
            speed = 1;
        }
    }

    // Sets the fractional length of the 2nd tap
    //   2/3 (0.66667) = Triplett
    //   3/4 (0.75) = Dotted Eighth
    inline void set2ndTapFraction(float tapFraction) {
        secondTapFraction = tapFraction;

        // For secondTap (if this changes we want to recalculate the second tap based on current delay setting)
        int32_t int_delay_secondTap = static_cast<int32_t>(delay_float * secondTapFraction);
        frac_secondTap = delay_float * secondTapFraction - static_cast<float>(int_delay_secondTap);
        delay_secondTap = static_cast<size_t>(int_delay_secondTap) < max_size ? int_delay_secondTap : max_size - 1;
    }

    /** sets the delay time in samples
        If a float is passed in, a fractional component will be calculated for interpolating the delay line.
    */
    inline void SetDelay(size_t delay) {
        frac_ = 0.0f;
        delay_ = delay < max_size ? delay : max_size - 1;
    }

    /** sets the delay time in samples
        If a float is passed in, a fractional component will be calculated for interpolating the delay line.
    */
    inline void SetDelay(float delay) {
        int32_t int_delay = static_cast<int32_t>(delay);
        frac_ = delay - static_cast<float>(int_delay);
        delay_ = static_cast<size_t>(int_delay) < max_size ? int_delay : max_size - 1;
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
